swaety/OCS/images/image_0_proto.png

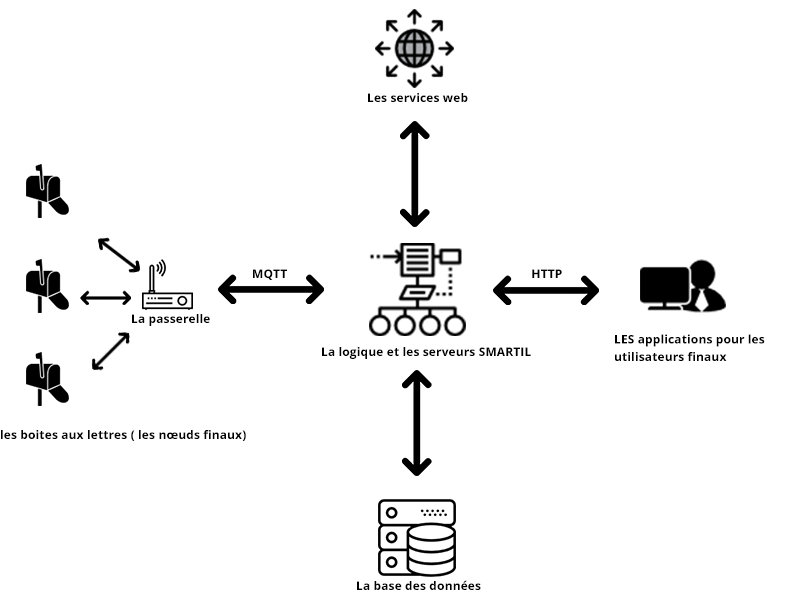
images/image_0_proto.png
