swaety/OCS/images/image_1_proto.jpg

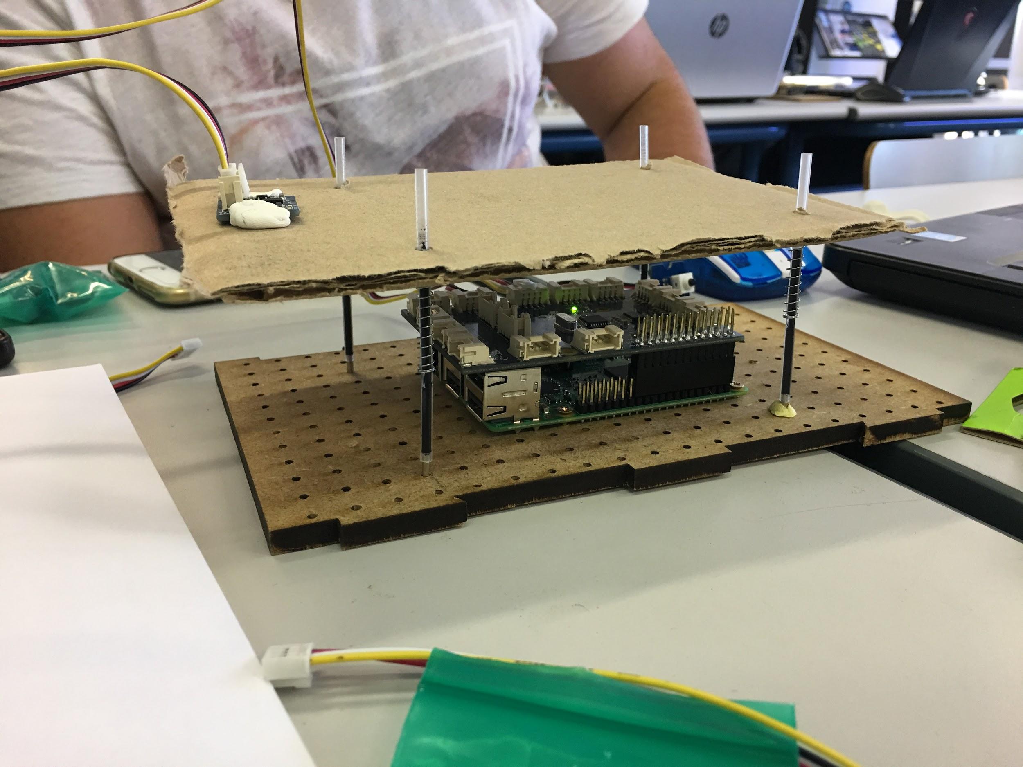
images/image_1_proto.jpg
