swaety/OCS/images/image_2_proto.jpg

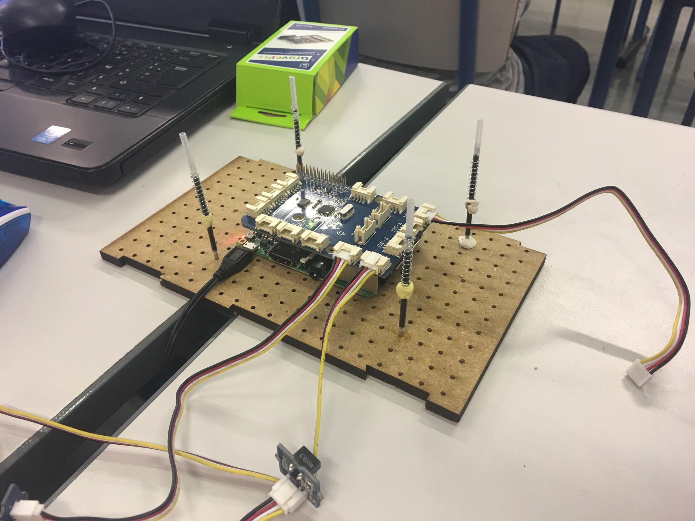
images/image_2_proto.jpg
