swaety/OCS/Sprint3/IHMWeb/styles/images/article.png

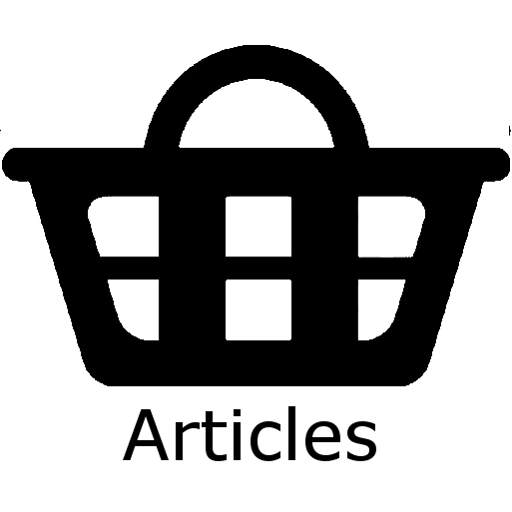
Sprint3/IHMWeb/styles/images/article.png
