swaety/OCS/Sprint3/IHMWeb/styles/images/back - Copie.png

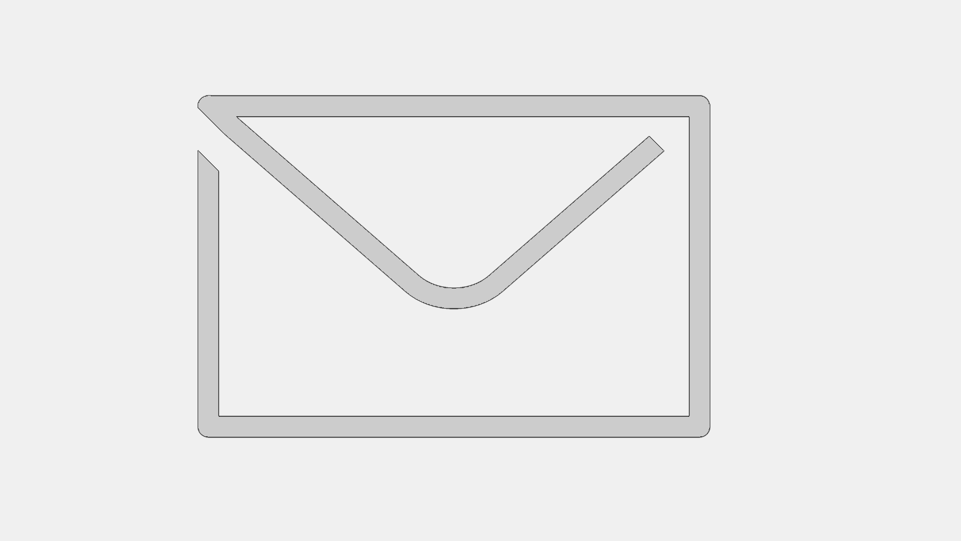
Sprint3/IHMWeb/styles/images/back - Copie.png
