swaety/OCS/Sprint3/IHMWeb/styles/images/ban.png

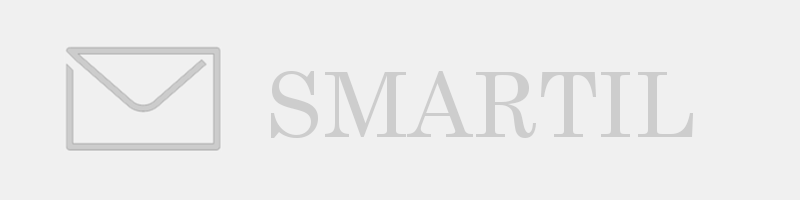
Sprint3/IHMWeb/styles/images/ban.png
