swaety/OCS/Sprint3/IHMWeb/styles/images/mail.png

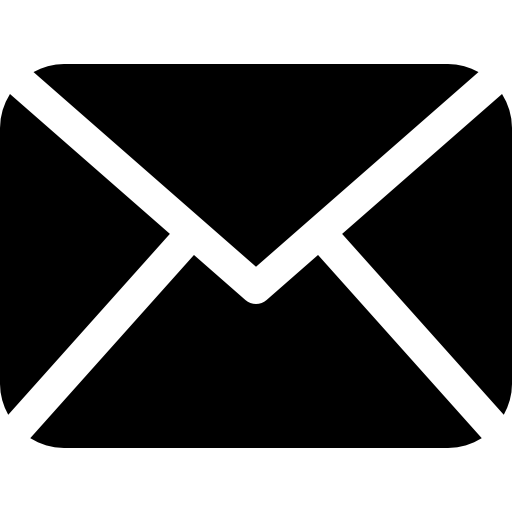
Sprint3/IHMWeb/styles/images/mail.png
